DesignedbyAmpersand/ESPkachu/IMG_2853.jpg

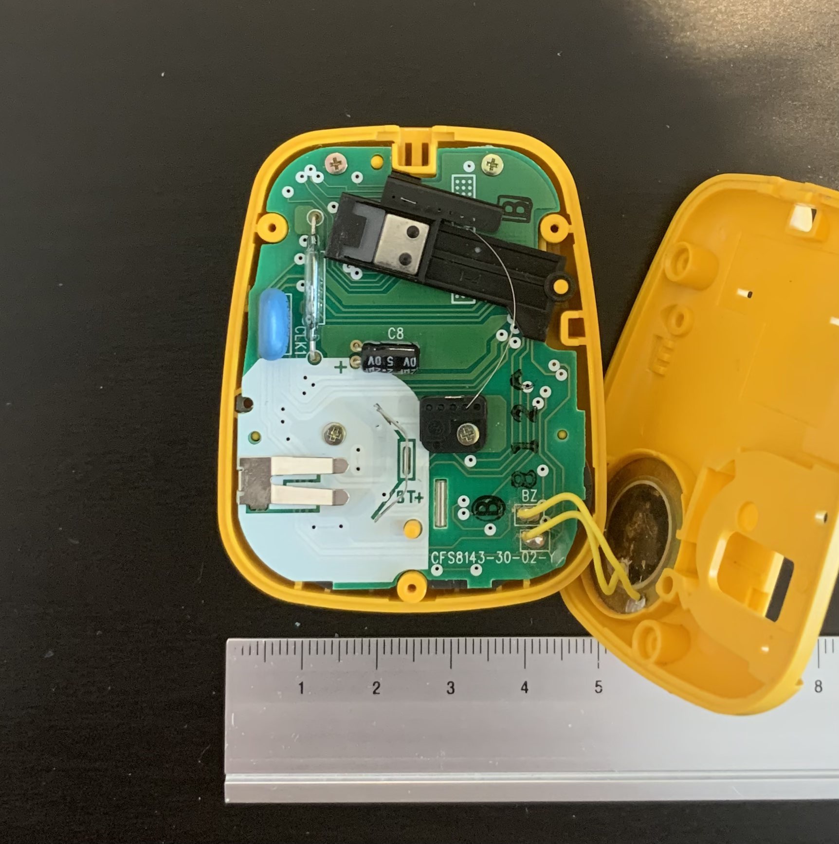
IMG_2853.jpg
